makotoworkshop/Pocket-SDVX-Pico-Makoto_edition/SOURCES/Graphics_Kicad/skin-rgb-300dpi_EDGES-CUT_XDA-Keycaps.png

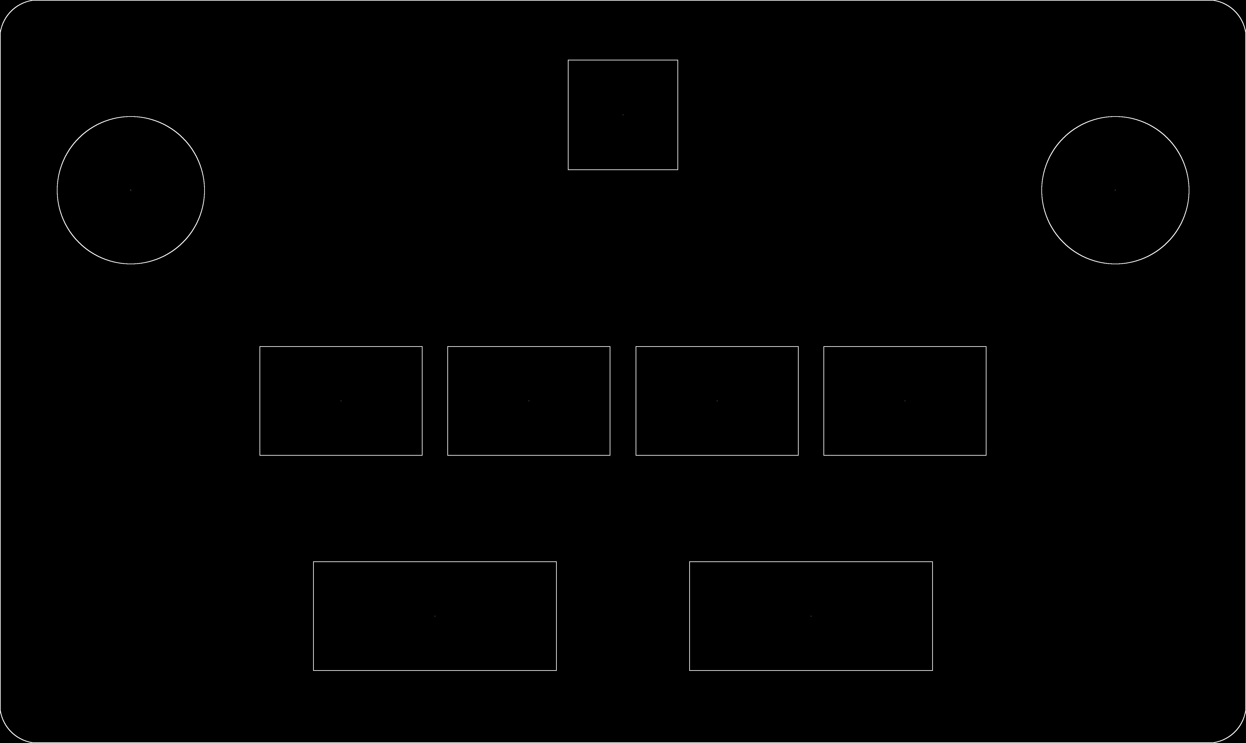
SOURCES/Graphics_Kicad/skin-rgb-300dpi_EDGES-CUT_XDA-Keycaps.png
