makotoworkshop/Pocket-SDVX-Pico-Makoto_edition/SOURCES/Graphics_Kicad/skin-rgb-300dpi_Mask.png

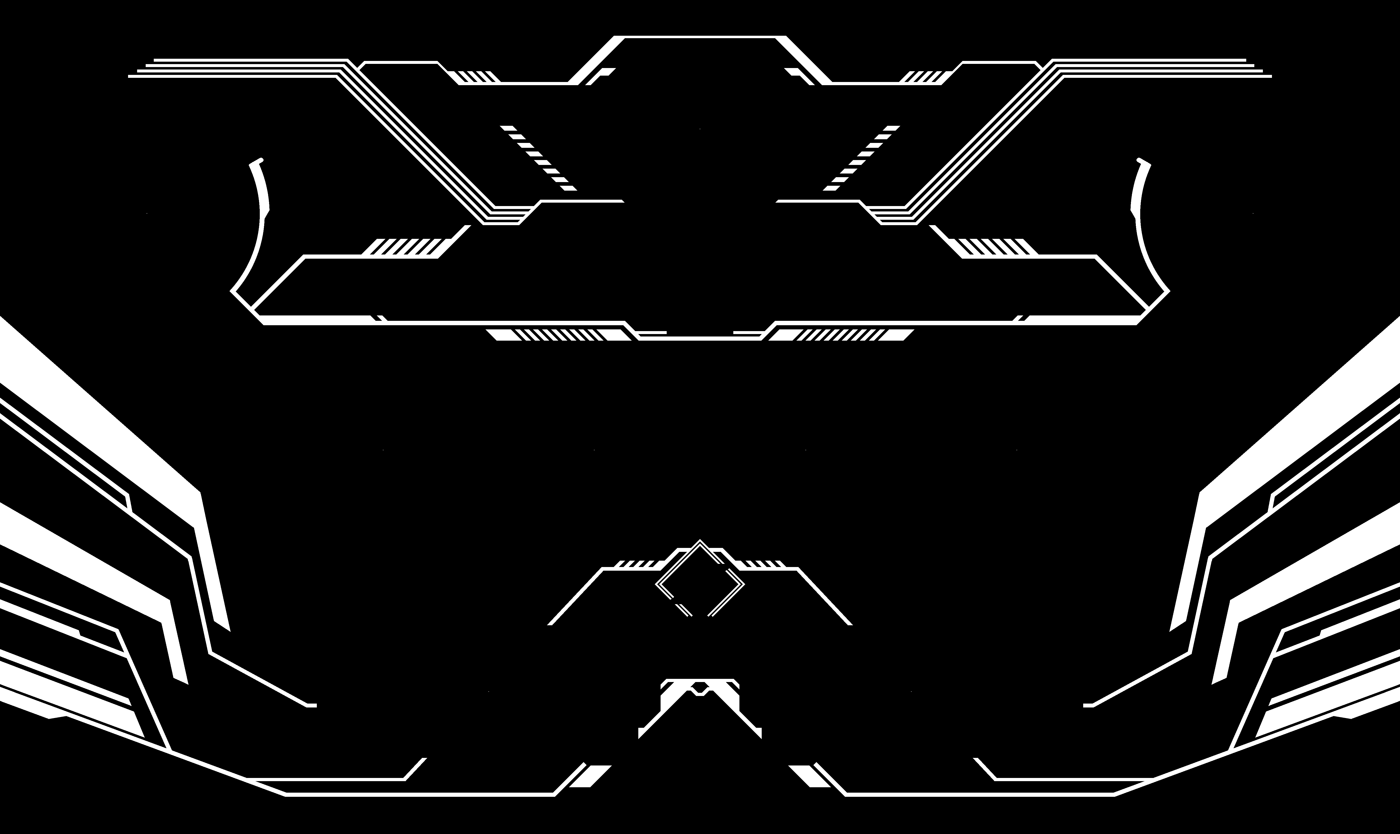
SOURCES/Graphics_Kicad/skin-rgb-300dpi_Mask.png
