makotoworkshop/Pocket-SDVX-Pico-Makoto_edition/SOURCES/PLATE3/No_3D_Support_Needed.png

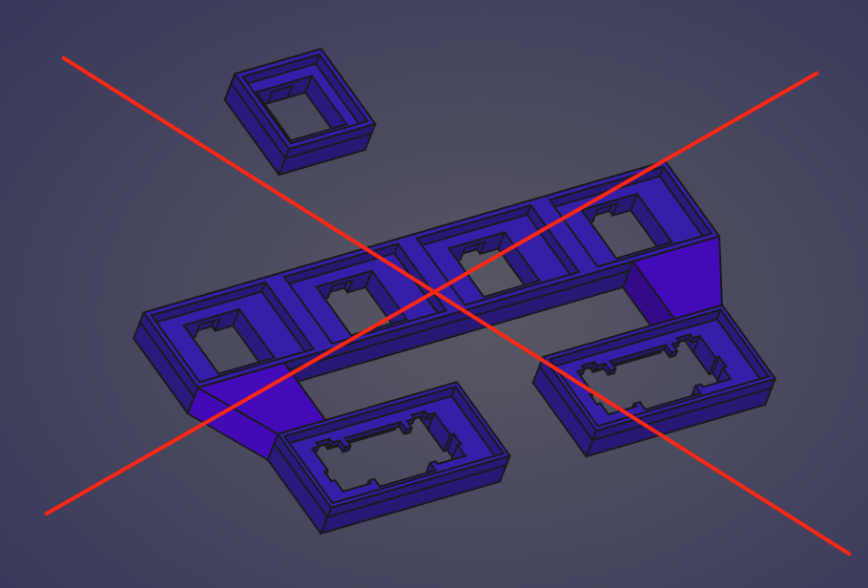
SOURCES/PLATE3/No_3D_Support_Needed.png
