makotoworkshop/Pocket-SDVX-Pico-Makoto_edition/SOURCES/PLATE3/Pocket SDVX Pico v4_02.png

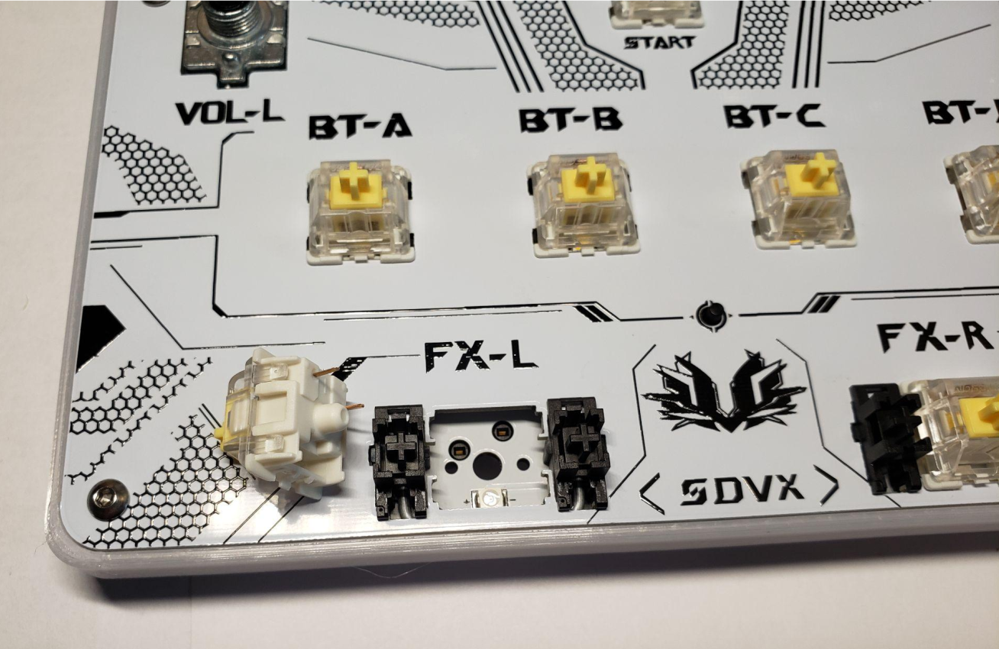
SOURCES/PLATE3/Pocket SDVX Pico v4_02.png
