makotoworkshop/Pocket-SDVX-Pico-Makoto_edition/SOURCES/PLATE3/Pocket SDVX Pico v5.jpg

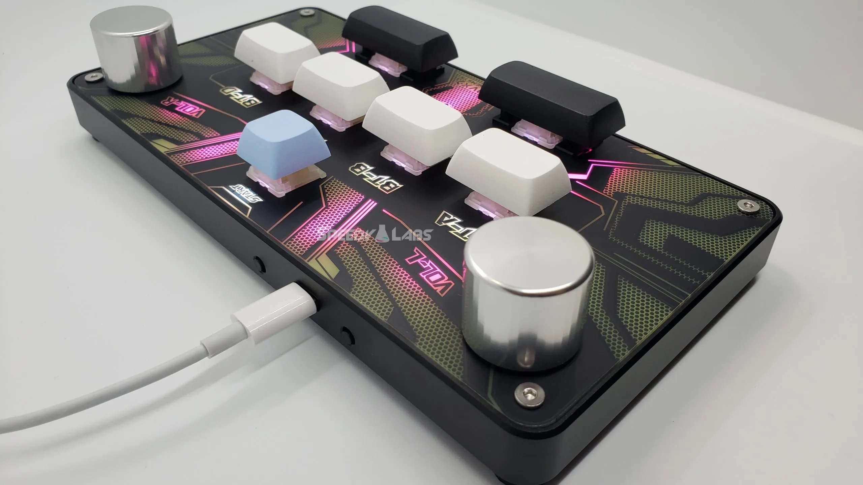
SOURCES/PLATE3/Pocket SDVX Pico v5.jpg
