makotoworkshop/Pocket-SDVX-Pico-Makoto_edition/SOURCES/PLATE/3D/Pocket-SDVX-Pico-Plate_Makoto_Blanc.png

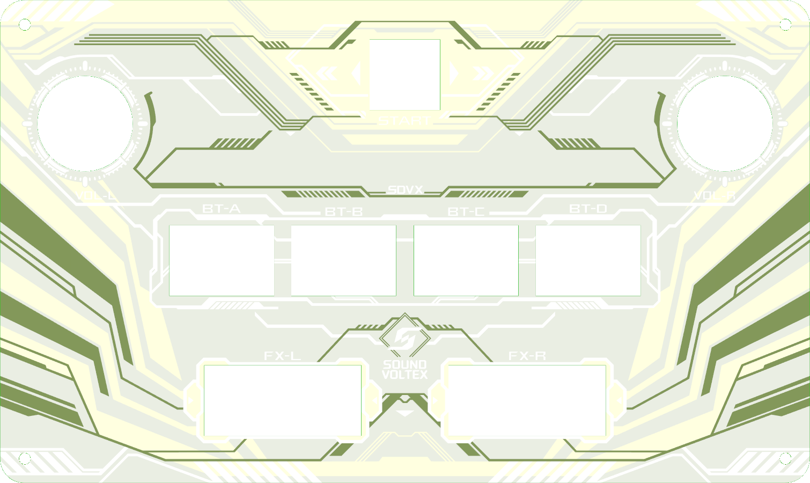
SOURCES/PLATE/3D/Pocket-SDVX-Pico-Plate_Makoto_Blanc.png
