makotoworkshop/Pocket-SDVX-Pico-Makoto_edition/SOURCES/PLATE/3D/Pocket-SDVX-Pico-Plate_Makoto.step

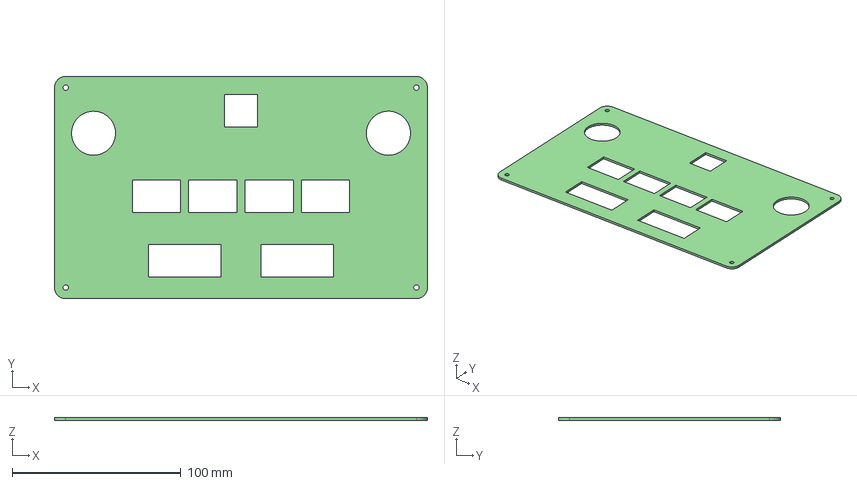
[picture p32: CAD file, 2025-12-27]
SOURCES/PLATE/3D/Pocket-SDVX-Pico-Plate_Makoto.step
220.9 x 131.7 x 1.60 mm
