makotoworkshop/Pocket-SDVX-Pico-Makoto_edition/PRODUCTION/3D_printables/Contour_Cadre/Pocket-SDVX-Pico-CASE_Makoto-BoitierCut_Contour_Gauche_3x3mm.stl

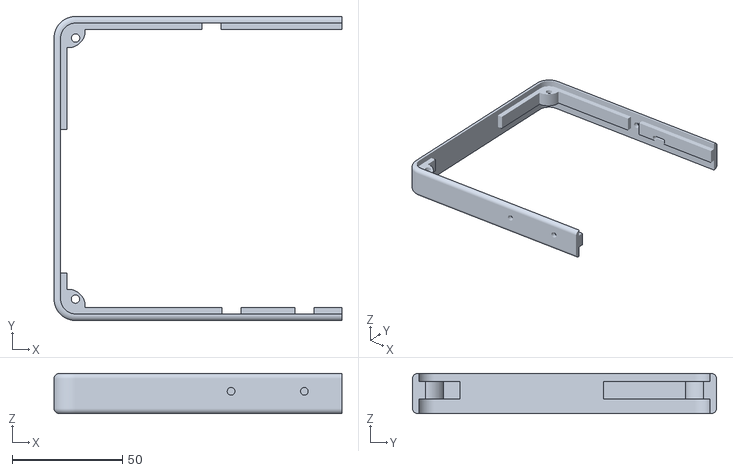
[picture p33: CAD file, 2025-12-27]
PRODUCTION/3D_printables/Contour_Cadre/Pocket-SDVX-Pico-CASE_Makoto-BoitierCut_Contour_Gauche_3x3mm.stl
130.6 x 137.9 x 18.2
