makotoworkshop/Pocket-SDVX-Pico-Makoto_edition/PRODUCTION/3D_printables/Plaque_Dessous_Fond/Pocket-SDVX-Pico-CASE_Makoto-BoitierCut_Fond_Gauche.stl

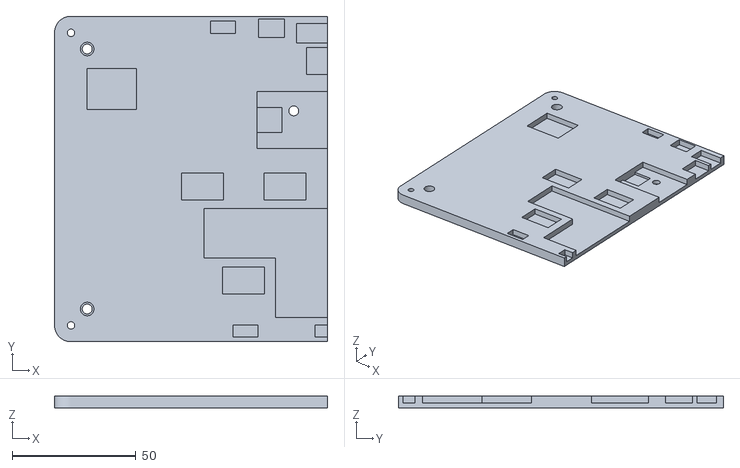
[picture p34: CAD file, 2025-12-27]
PRODUCTION/3D_printables/Plaque_Dessous_Fond/Pocket-SDVX-Pico-CASE_Makoto-BoitierCut_Fond_Gauche.stl
110.5 x 131.7 x 5.00
