makotoworkshop/Pocket-SDVX-Pico-Makoto_edition/SOURCES/PCB/3D/xda-keycap-set-model_files/XDA_2U_spanning-2-switches.stl

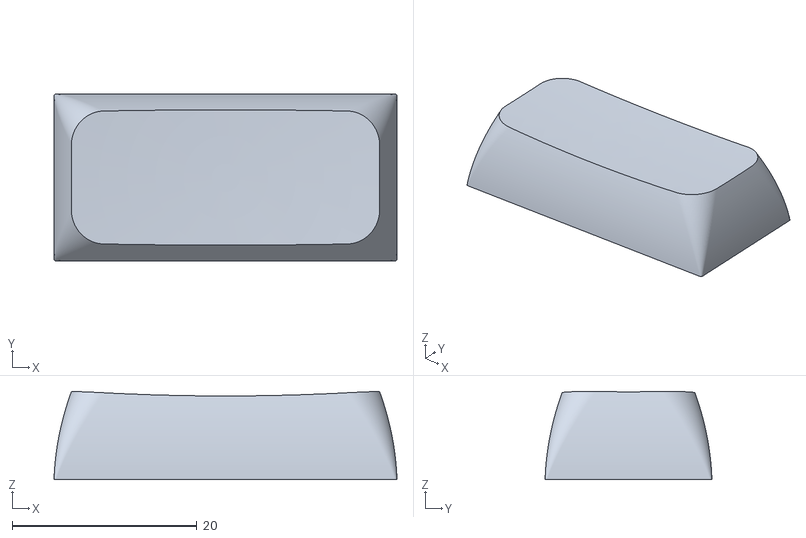
[picture p35: CAD file, 2025-12-27]
SOURCES/PCB/3D/xda-keycap-set-model_files/XDA_2U_spanning-2-switches.stl
37.1 x 18.0 x 9.53
