makotoworkshop/Pocket-SDVX-Pico-Makoto_edition/PRODUCTION/3D_printables/Plaque_Dessous_Fond/Pocket-SDVX-Pico-CASE_Makoto-BoitierPlaquettes Raccord02.stl

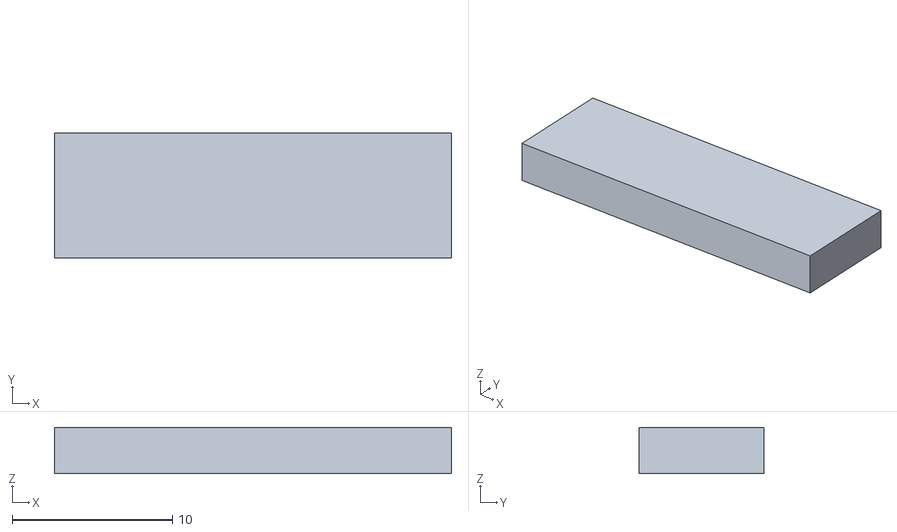
[picture p37: CAD file, 2025-12-27]
PRODUCTION/3D_printables/Plaque_Dessous_Fond/Pocket-SDVX-Pico-CASE_Makoto-BoitierPlaquettes Raccord02.stl
24.8 x 7.80 x 2.90
