makotoworkshop/Pocket-SDVX-Pico-Makoto_edition/SOURCES/PCB/3D/xda-keycap-set-model_files/XDA_1.5U.stl

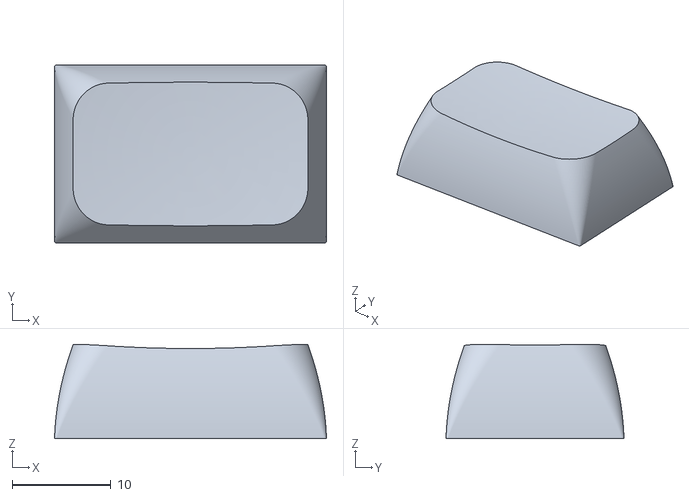
[picture p38: CAD file, 2025-12-27]
SOURCES/PCB/3D/xda-keycap-set-model_files/XDA_1.5U.stl
27.6 x 18.0 x 9.57
