makotoworkshop/Pocket-SDVX-Pico-Makoto_edition/SOURCES/PCB/3D/xda-keycap-set-model_files/XDA_1.75U.stl

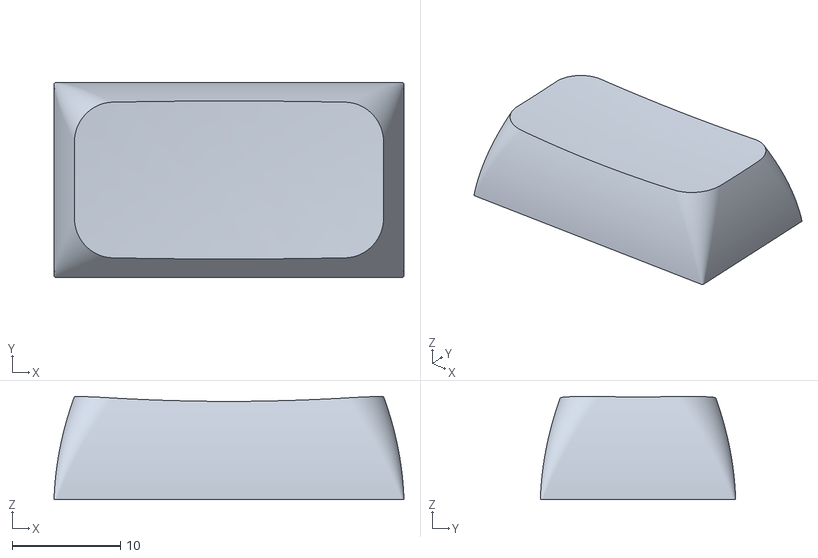
[picture p39: CAD file, 2025-12-27]
SOURCES/PCB/3D/xda-keycap-set-model_files/XDA_1.75U.stl
32.3 x 18.0 x 9.54
