makotoworkshop/Pocket-SDVX-Pico-Makoto_edition/SOURCES/PCB/3D/xda-keycap-set-model_files/XDA_2.5U_S.stl

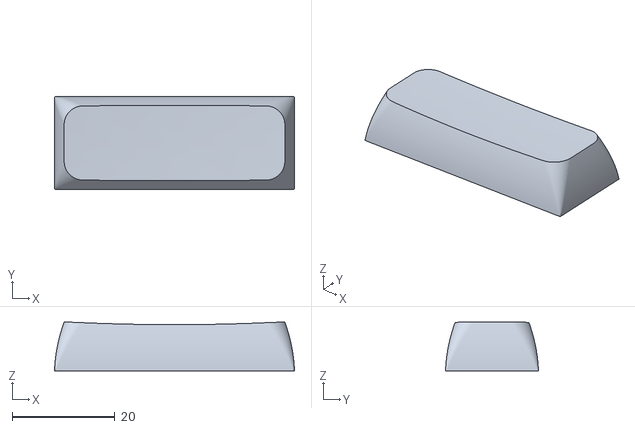
[picture p41: CAD file, 2025-12-27]
SOURCES/PCB/3D/xda-keycap-set-model_files/XDA_2.5U_S.stl
46.6 x 18.0 x 9.51
