makotoworkshop/Pocket-SDVX-Pico-Makoto_edition/SOURCES/PCB/3D/xda-keycap-set-model_files/XDA_1.25U_2U_square-iso-enter.stl

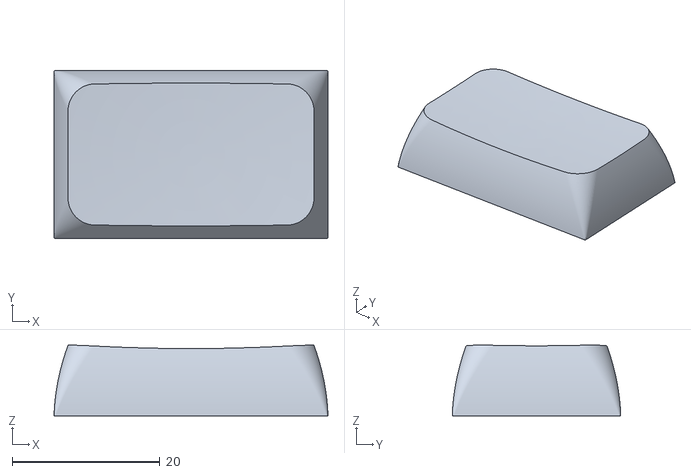
[picture p43: CAD file, 2025-12-27]
SOURCES/PCB/3D/xda-keycap-set-model_files/XDA_1.25U_2U_square-iso-enter.stl
37.1 x 22.8 x 9.58
