makotoworkshop/Pocket-SDVX-Pico-Makoto_edition/SOURCES/PCB/3D/xda-keycap-set-model_files/XDA_1.25U_fake-stepped-caps.stl

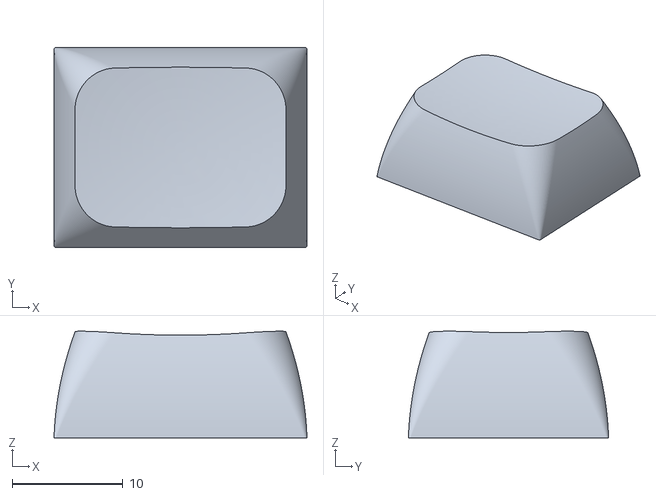
[picture p45: CAD file, 2025-12-27]
SOURCES/PCB/3D/xda-keycap-set-model_files/XDA_1.25U_fake-stepped-caps.stl
22.8 x 18.0 x 9.61
